Toruitas/thinkingcap/img/wk10/IMG_8880.jpeg

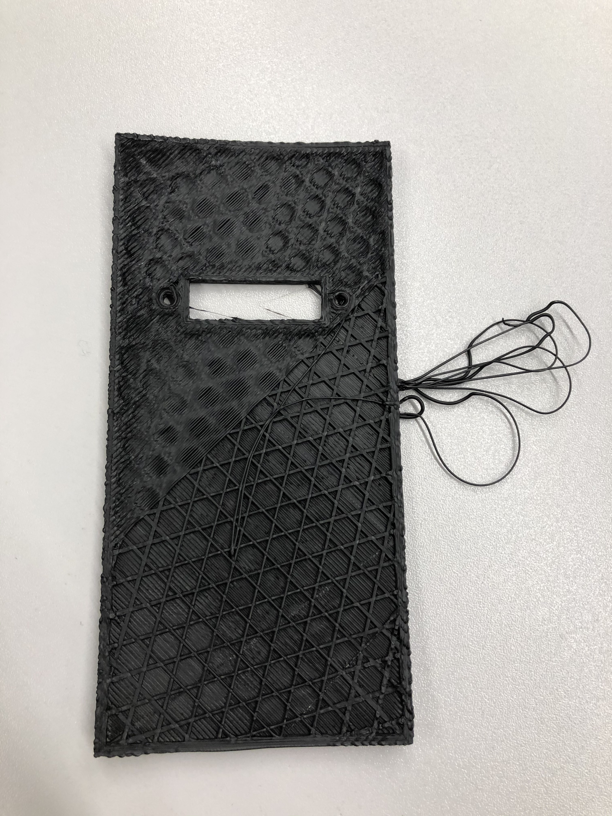
img/wk10/IMG_8880.jpeg
