Toruitas/thinkingcap/img/wk10/IMG_8912.jpeg

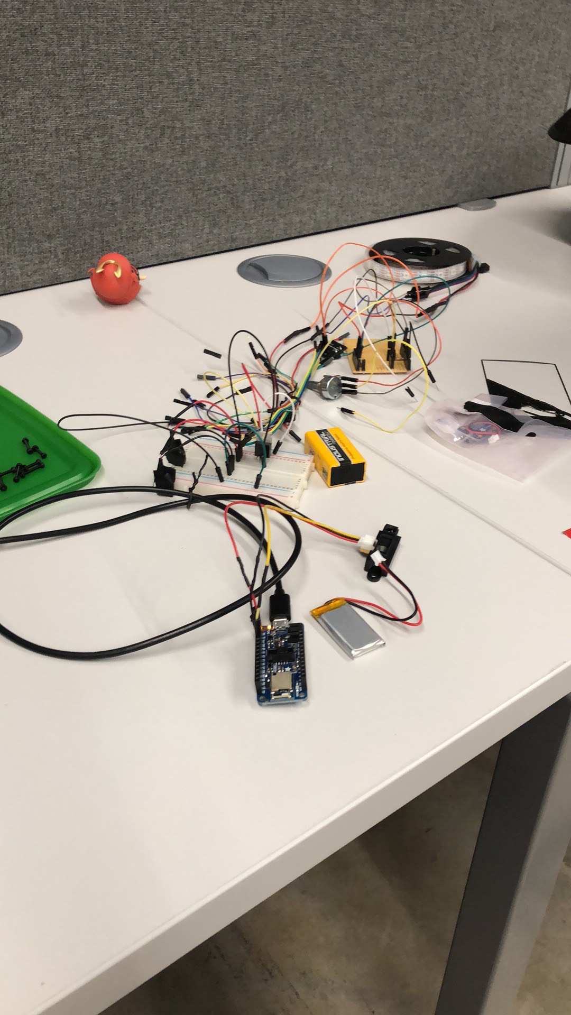
img/wk10/IMG_8912.jpeg
