Toruitas/thinkingcap/img/wk11/BBB.JPG

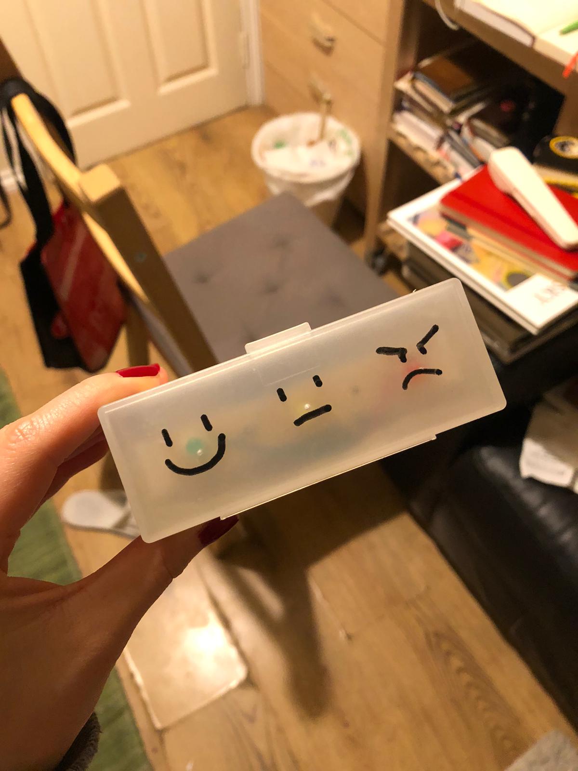
img/wk11/BBB.JPG
