Toruitas/thinkingcap/serial_version/local_connection_serial.py

import serial
import argparse
import math
import time
import json
from pythonosc.dispatcher import Dispatcher
from pythonosc import osc_server
import asyncio
import datetime
from contextvars import ContextVar

# Arduino constants for dev
ARD_PORT = "/dev/ttyACM0" # COM3 or /dev/ttyACM0
# Osc server constants
IP = "127.0.0.1"
OSC_PORT = 5005

# https://docs.python.org/3.7/library/contextvars.html
# Context Vars work great with asyncio
focused = ContextVar("focused", default=False)  # focused = False
# since focused can be overriden, true focus state is stored in a separate var
mentally_focused = ContextVar("mentally_focused", default=False)
wearing = ContextVar("wearing", default=False)  # wearing = False
hat_running = ContextVar("hat_running", default=False)  # running = True
user_override = ContextVar("user_override", default=False)  # user_override = False
connected = ContextVar("connected", default=False)
last_reading = ContextVar("last_reading", default=datetime.datetime.now())
attention_lvl = ContextVar("attn", default=0.0)  # for storing the current level of attention



def concentration_handler(unused_addr:str, fixed_argument, concentration):
    """
    This is called every time data comes in by the OSC dispatcher.
    https://python-osc.readthedocs.io/en/latest/dispatcher.html
    :param unused_addr: the given address that's associated with this "view"
    :param args: anything extra
    :param concentration: values of concentration
    :return:
    """
    # print("Current attention level: ", concentration)
    # if concentration >= 0.5 and mentally_focused.get() is False:
    #     mentally_focused.set(True)
    #     if not user_override.get():
    #         focused.set(mentally_focused.get())
    #     print("Focused, you bad mofo, you. Look at that.")
    #     return mentally_focused.get()
    # else:
    #     mentally_focused.set(False)
    #     if not user_override.get():
    #         focused.set(mentally_focused.get())
    #     return mentally_focused.get()
    a_s = fixed_argument[0]

    print("Current attention level: ", concentration)
    if concentration >= 0.5:
        a_s.mentally_focused = True
        if not a_s.user_override:
            a_s.focused = a_s.mentally_focused
        # print("Focused, you bad mofo, you. Look at that.")
        # return a_s.mentally_focused
    else:
        a_s.mentally_focused = False
        if not a_s.user_override:
            a_s.focused = a_s.mentally_focused
        # return a_s.mentally_focused


async def loop(ser, async_state):

    while async_state.hat_running:
    # while hat_running.get():
        # user_input = input('Test control of Arduino? f for focus; anything else to quit.')
        #
        # if user_input == 'f':
        #     # This should change "focused" to true here and on the Ard.
        #     # Through setting "focused" on the Ard, it will vibrate, light up, etc.
        #     focused.set(True)
        #     ser.write(b'f')
        #
        # if user_input != 'f':
        #     hat_running.set(False)   # shut it down on next loop
        #     ser.write(b'x')  # o for off.

        state = ser.readline()
        if state:
            # connection made, update the variables
            update_server_state(state, async_state)
        else:
            update_client_state(ser, async_state)
        await asyncio.sleep(.1)


def update_server_state(state: str, async_state):
    """
    Takes a new state from the Ard and mirrors it on this server.
    Uses set.state since we're in async land
    :param state: string JSON object
    :return: dict object of the state
    """
    # https://stackoverflow.com/questions/26838953/python-read-from-serial-port-and-encode-as-json
    try:
        state = json.loads(state)
    except json.decoder.JSONDecodeError as error:
        print(state)  # this just prints whatever the message actually is
        return False  # early return to prevent the rest of the fn from running

    if type(state) == dict:
        # hat_running.set(True)
        # connected.set(True)
        # focused.set(state["focused"])
        # wearing.set(state["wearing"])
        # user_override.set(state["userOverride"])
        # last_reading.set(datetime.datetime.now())

        async_state.hat_running = True
        async_state.connected = True
        async_state.focused = state["focused"]
        async_state.wearing = state["wearing"]
        async_state.user_override = state["userOverride"]
        async_state.last_reading = datetime.datetime.now()

        state_dict = context_vars_to_state_dict(async_state)

        # log the update to the console
        print("Server state updated to: ")
        print(state_dict)

        # no real reason to return, but doing anyway
        return state_dict
    else:
        print(state)


def update_client_state(ser, async_state):
    """
    Update the Arduino client.
    https://stackoverflow.com/questions/22275079/pyserial-write-wont-take-my-string
    :return:
    """
    state = context_vars_to_state_dict(async_state)
    state_json = json.dumps(state)  # dump to a JSON string

    ser.write(state_json.encode())  # encode
    # Log to the console
    print("Client state updated to: ")
    print(state_json)


def context_vars_to_state_dict(async_state) -> dict:
    """
    Convenience fn to turn the context variables into a dictionary,
    :return:
    """
    # print(mentally_focused.get())
    # state_dict = {
    #     "focused": focused.get(),
    #     "mentally_focused": mentally_focused.get(),
    #     "wearing": wearing.get(),
    #     "hat_running": hat_running.get(),
    #     "connected": connected.get(),
    #     "user_override": user_override.get(),
    #     "last_reading": last_reading.get()
    # }

    state_dict = {
        "focused": async_state.focused,
        "mentally_focused": async_state.mentally_focused,
        "wearing": async_state.wearing,
        "hat_running": async_state.hat_running,
        "connected": async_state.connected,
        "user_override": async_state.user_override,
        "last_reading": async_state.last_reading
    }

    return state_dict


def make_connection(ser, async_state):
    """
    Using the given serial connection, attempts to start reading data. If it tries long enough, it'll time out.
    :param ser:
    :return: True if connected
    """
    print("making a connection")
    while not hat_running.get():
        state = ser.readline()
        if state:
            # connection made, update the variables
            updated = update_server_state(state, async_state)
            if updated:
                print("Connected to Thinking Cap. Don't let your dreams be dreams!")
            return True
        # if timeout todo: make a timeout here for connections.


async def init_main():
    """

    https://python-osc.readthedocs.io/en/latest/server.html#async-server
    https://web.archive.org/web/20170809181820/http://developer.choosemuse.com/research-tools-example/grabbing-data-from-museio-a-few-simple-examples-of-muse-osc-servers
    https://addshore.com/2018/06/python3-using-some-shared-state-in-2-async-methods/
    :return:
    """
    # making a super ghetto state to share b/w the two async contexts
    # based on solution in https://addshore.com/2018/06/python3-using-some-shared-state-in-2-async-methods/
    async_state = type('', (), {})()
    async_state.focused = False
    async_state.mentally_focused = False
    async_state.wearing = False
    async_state.hat_running = False
    async_state.user_override = False
    async_state.last_reading = datetime.datetime.now()
    async_state.attention_lvl = 0.0

    # Prepare the serial port
    # make_connection
    ser = serial.Serial(ARD_PORT, baudrate=9600, timeout=1)
    connection_made = make_connection(ser, async_state)

    if connection_made:
        # with the connection made and inital state set, can start the main loops.
        # https://python-osc.readthedocs.io/en/latest/dispatcher.html
        # https://python-osc.readthedocs.io/en/latest/server.html#async-server
        event_loop_local = asyncio.get_event_loop()
        dispatcher = Dispatcher()
        dispatcher.map("/muse/elements/experimental/concentration", concentration_handler, async_state)
        # creates an OSC server that's Async.
        server = osc_server.AsyncIOOSCUDPServer((IP, OSC_PORT), dispatcher, event_loop_local)
        transport, protocol = await server.create_serve_endpoint()  # Create datagram endpoint and start serving

        await loop(ser, async_state)  # Enter main loop of program.

        transport.close()  # Clean up serve endpoint

event_loop = asyncio.new_event_loop()
asyncio.set_event_loop(event_loop)
asyncio.run(init_main())
